jefferzn2001/RoSHI-Hardware/3D Prints/IMU_Holder/Print/top.STL

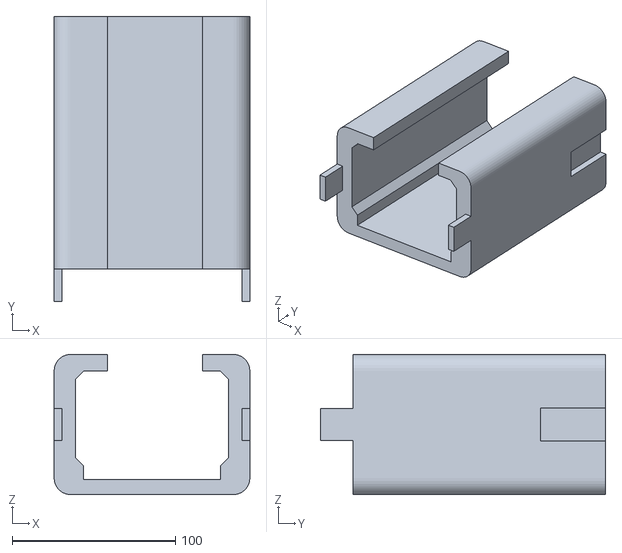
[picture p12: CAD file, 2026-04-07]
3D Prints/IMU_Holder/Print/top.STL
120.0 x 174.8 x 85.8
